aeroseed/urbolienne/2D drawings/DXF/ASD-US000015 - Axe-girouette.DXF

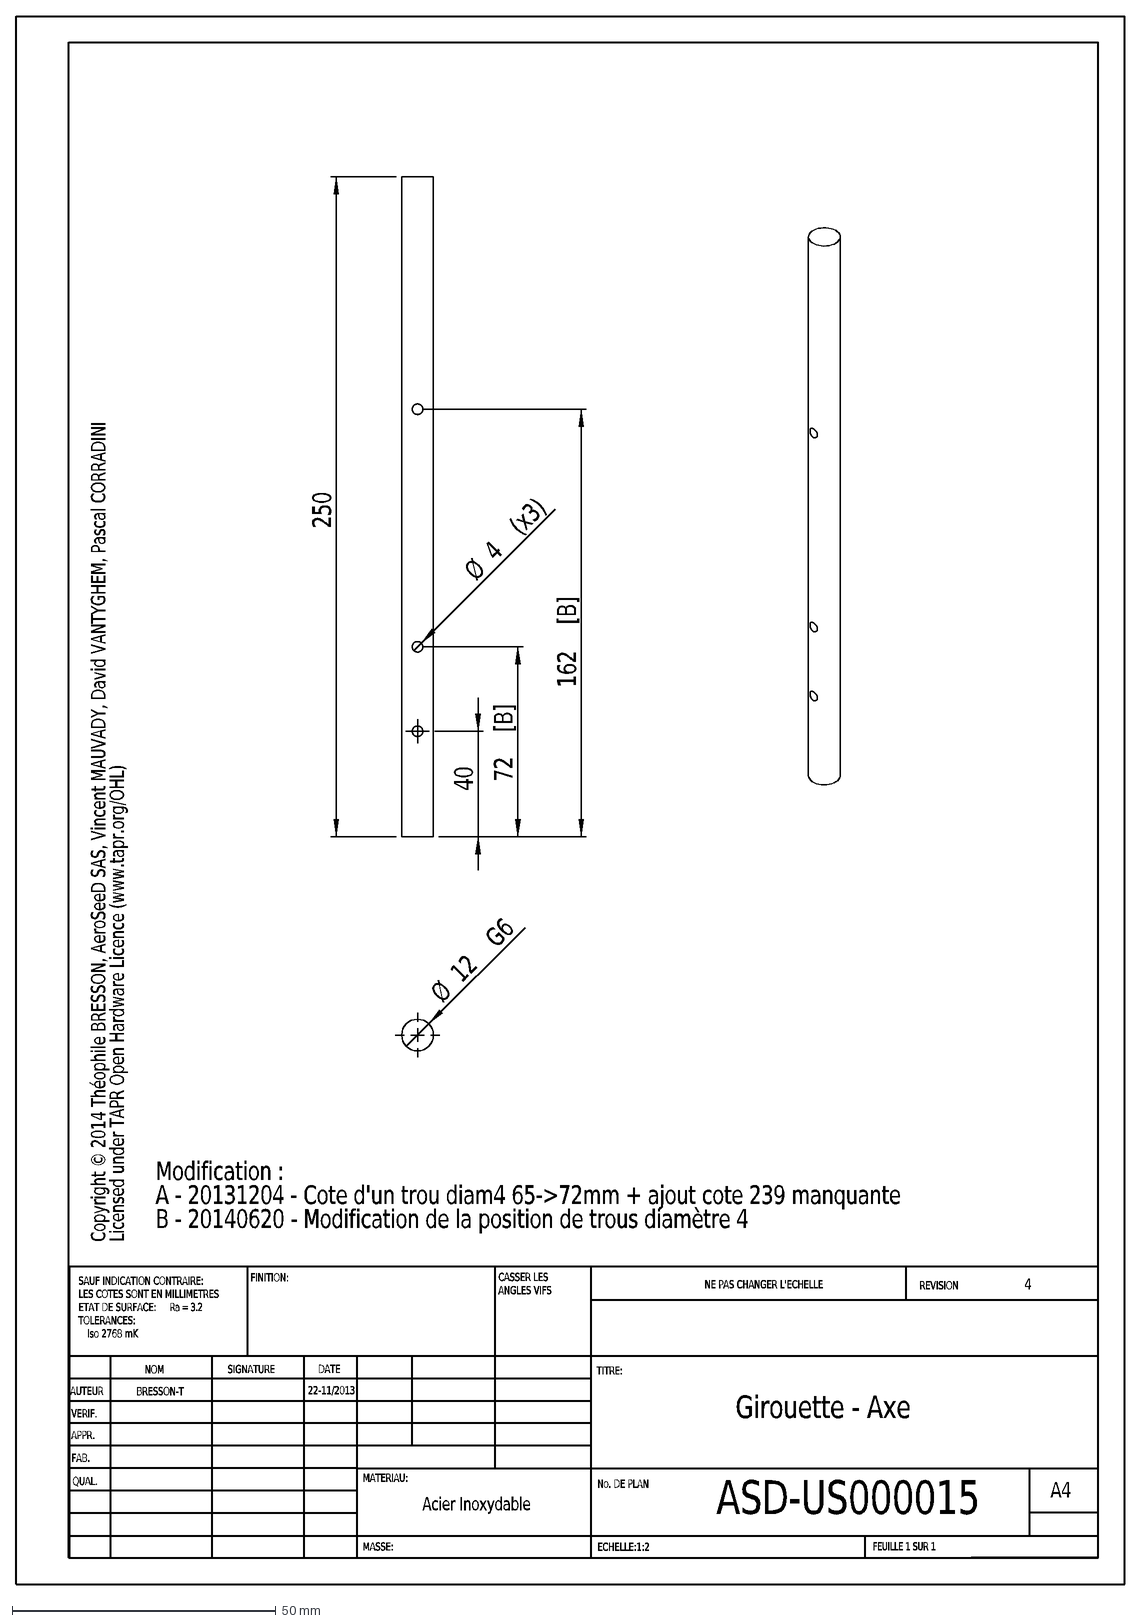
[picture p12: CAD file, 2014-06-24]
2D drawings/DXF/ASD-US000015 - Axe-girouette.DXF
Modification :
A - 20131204 - Cote d'un trou diam4 65->72mm + ajout cote 239 manquante
B - 20140620 - Modification de la position de trous diamètre 4
Copyright © 2014 Théophile BRESSON, AeroSeeD SAS, Vincent MAUVADY, David VANTYGHEM, Pascal CORRADINI
Licensed under TAPR Open Hardware Licence (www.tapr.org/OHL)
4
Girouette - Axe
ASD-US000015
22-11/2013
BRESSON-T
MASSE:
Acier Inoxydable
A4
FEUILLE 1 SUR 1
ECHELLE:1:2
No. DE PLAN
TITRE:
REVISION
NE PAS CHANGER L'ECHELLE
MATERIAU:
DATE
SIGNATURE
NOM
CASSER LES
ANGLES VIFS
FINITION:
QUAL.
FAB.
APPR.
VERIF.
AUTEUR
SAUF INDICATION CONTRAIRE:
LES COTES SONT EN MILLIMETRES
ETAT DE SURFACE:
Ra = 3.2
TOLERANCES:
Iso 2768 mK
40
250
72
[B]
Ø
(x3)
162
12
G6
