aeroseed/urbolienne/2D drawings/PDF/ASD-US000015 - Axe-girouette.PDF

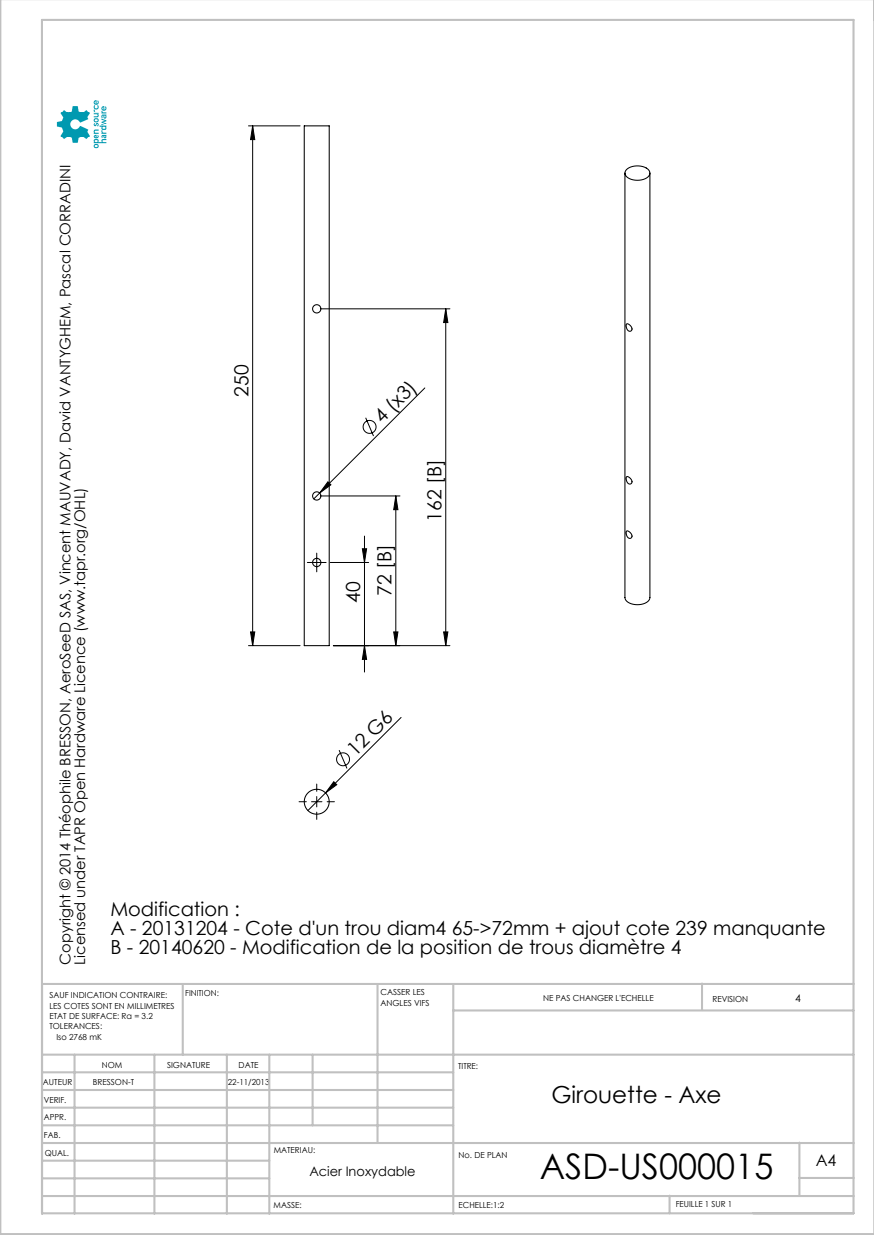
[picture p19: page 1]
ECHELLE:1:2; FEUILLE 1 SUR 1; NE PAS CHANGER L'ECHELLE; REVISION; CASSER LES ANGLES VIFS

Copyright © 2014 Théophile BRESSON, AeroSeeD SAS, Vincent MAUVADY, David VANTYGHEM, Pascal CORRADINI

Licensed under TAPR Open Hardware Licence (www.tapr.org/OHL)

Modification :
A - 20131204 - Cote d'un trou diam4 65->72mm + ajout cote 239 manquante
B - 20140620 - Modification de la position de trous diamètre 4

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

NOM | SIGNATURE | DATE | | | | TITRE: Girouette - Axe
QUAL. | | | | MATERIAU: Acier Inoxydable | ASD-US000015 No. DE PLAN | A4

AUTEUR | BRESSON-T | | 22-11/2013
VERIF.
APPR.
FAB.
