aeroseed/urbolienne/2D drawings/PDF/ASD-US000028 - Alternateur-rotor-CORADINI.PDF

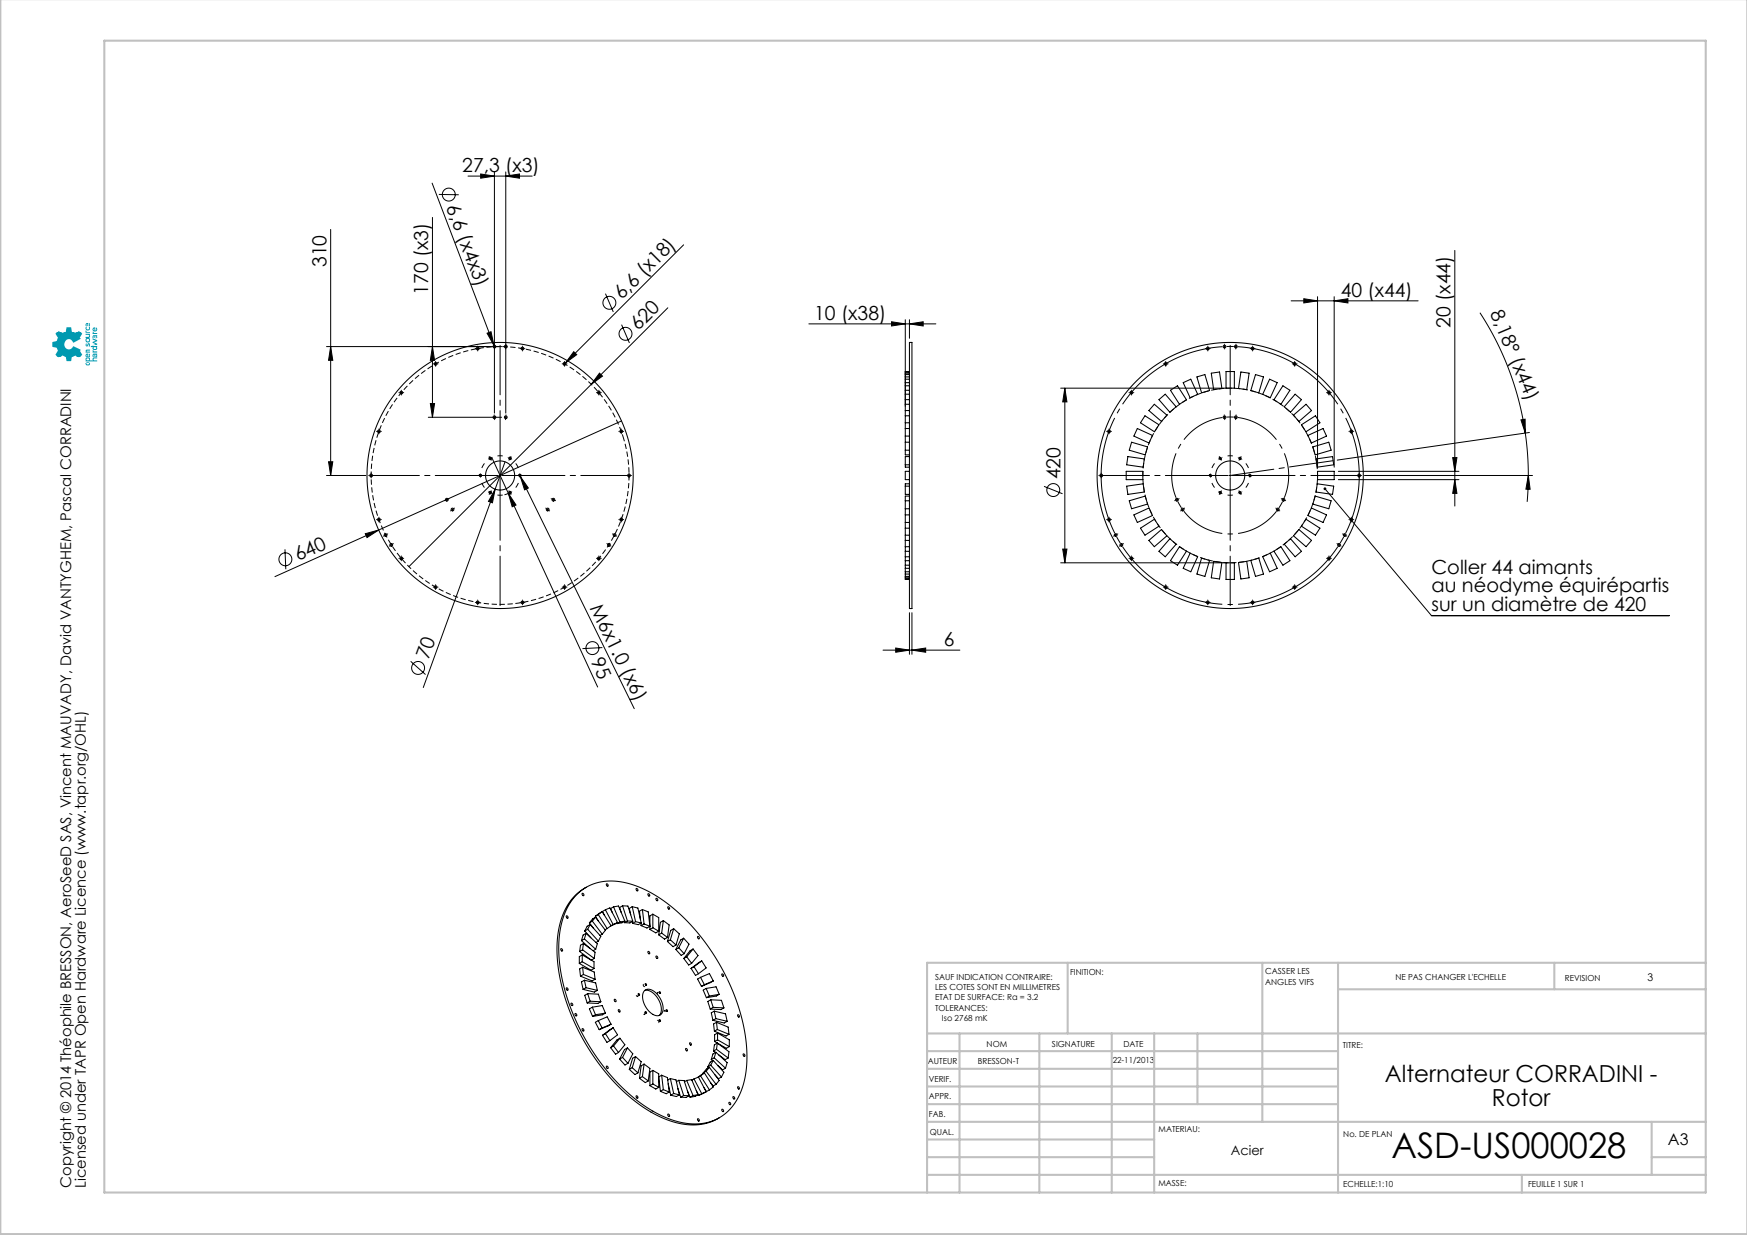
[picture p20: page 1]
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

Copyright © 2014 Théophile BRESSON, AeroSeeD SAS, Vincent MAUVADY, David VANTYGHEM, Pascal CORRADINI

Coller 44 aimants
au néodyme équirépartis
sur un diamètre de 420

Licensed under TAPR Open Hardware Licence (www.tapr.org/OHL)

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

NOM | SIGNATURE | DATE | | | | TITRE: Alternateur CORRADINI -Rotor
QUAL. | | | | MATERIAU: Acier | ASD-US000028 No. DE PLAN | A3

AUTEUR | BRESSON-T | | 22-11/2013
VERIF.
APPR.
FAB.
