aeroseed/urbolienne/2D drawings/PDF/ASD-US000031 - Arbre-transmission-pale.PDF

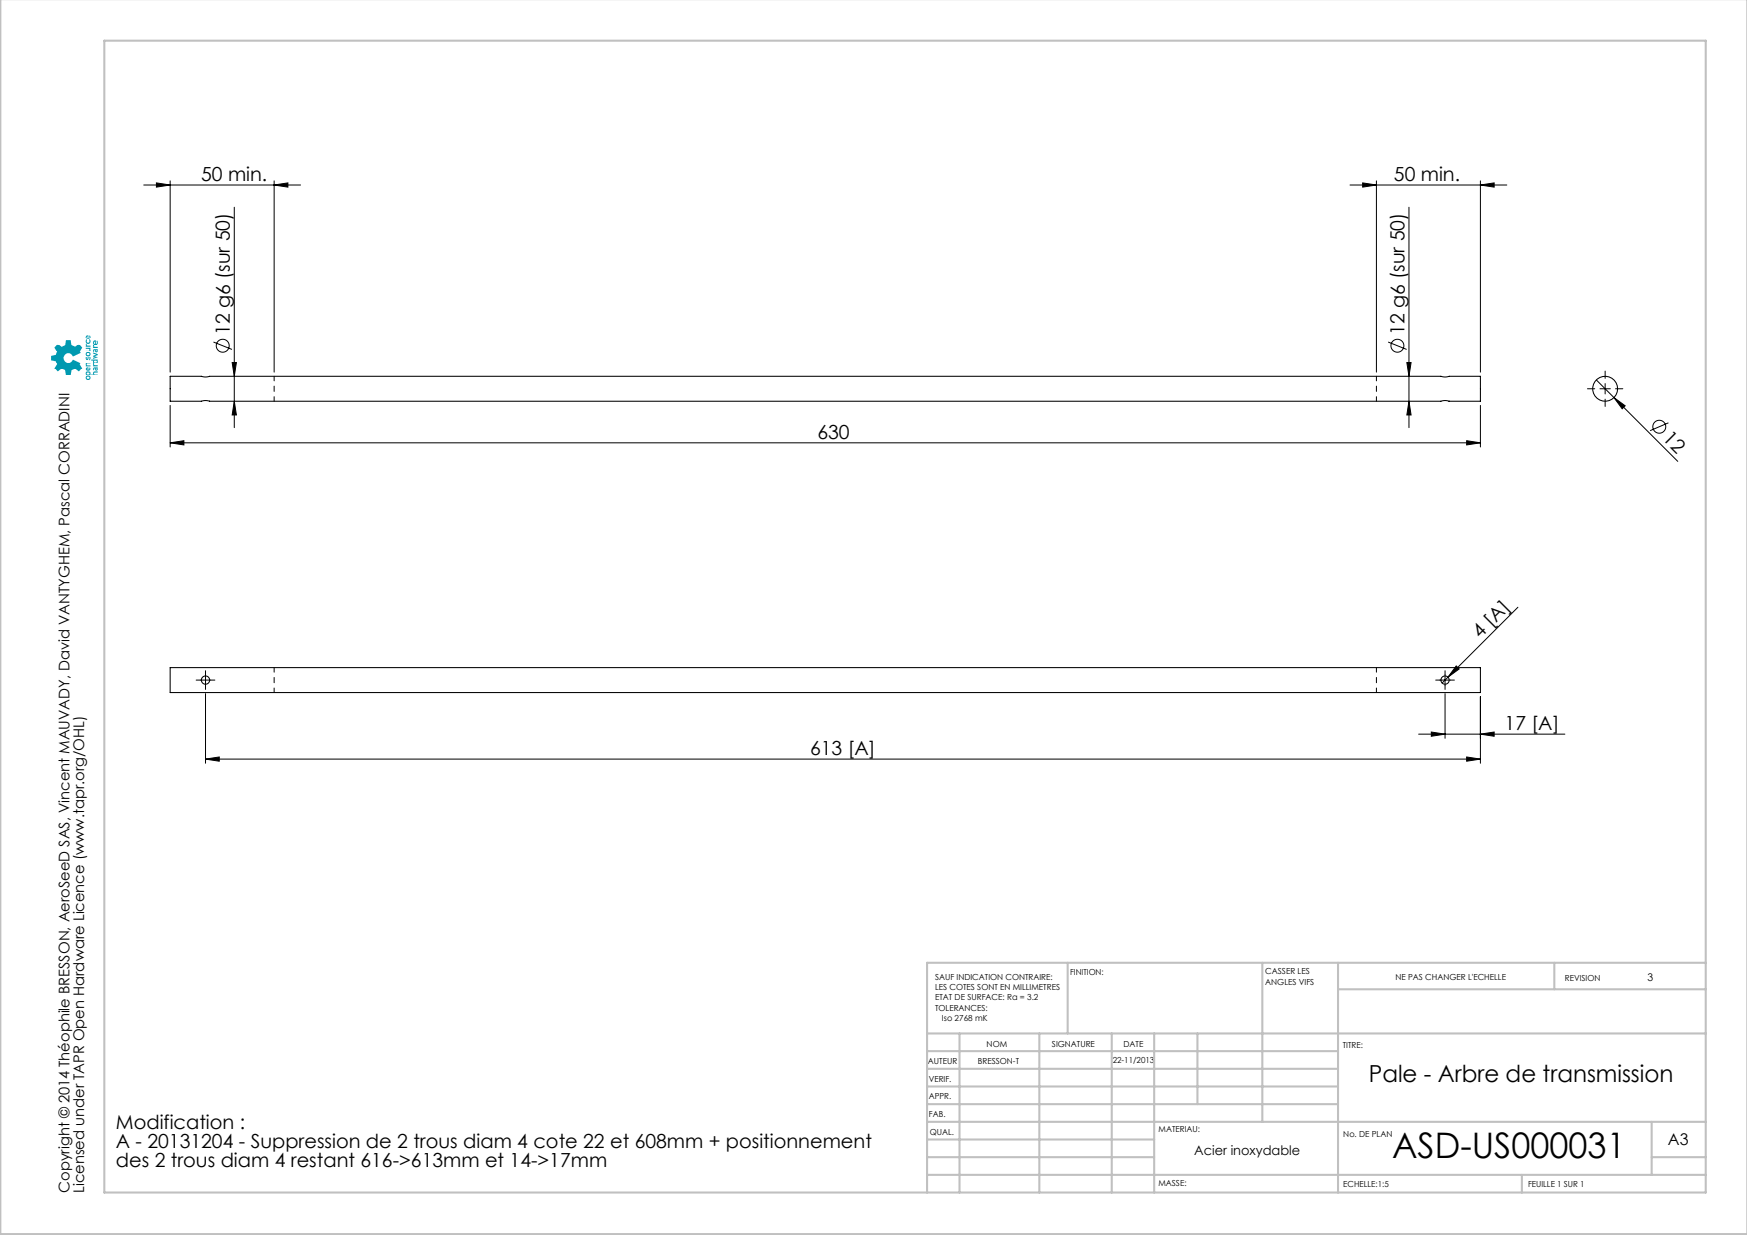
[picture p21: page 1]
12 g6 (sur 50); 50 min.; ECHELLE:1:5; FEUILLE 1 SUR 1; NE PAS CHANGER L'ECHELLE; REVISION; CASSER LES ANGLES VIFS

Copyright © 2014 Théophile BRESSON, AeroSeeD SAS, Vincent MAUVADY, David VANTYGHEM, Pascal CORRADINI

Licensed under TAPR Open Hardware Licence (www.tapr.org/OHL)

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

NOM | SIGNATURE | DATE | | | | TITRE: Pale - Arbre de transmission
QUAL. | | | | MATERIAU: Acier inoxydable | ASD-US000031 No. DE PLAN | A3

AUTEUR | BRESSON-T | | 22-11/2013
VERIF.
APPR.
FAB.

Modification :
A - 20131204 - Suppression de 2 trous diam 4 cote 22 et 608mm + positionnement
des 2 trous diam 4 restant 616->613mm et 14->17mm
