aeroseed/urbolienne/2D drawings/PDF/ASD-US000036 - Plateau-Axe-fixe.PDF

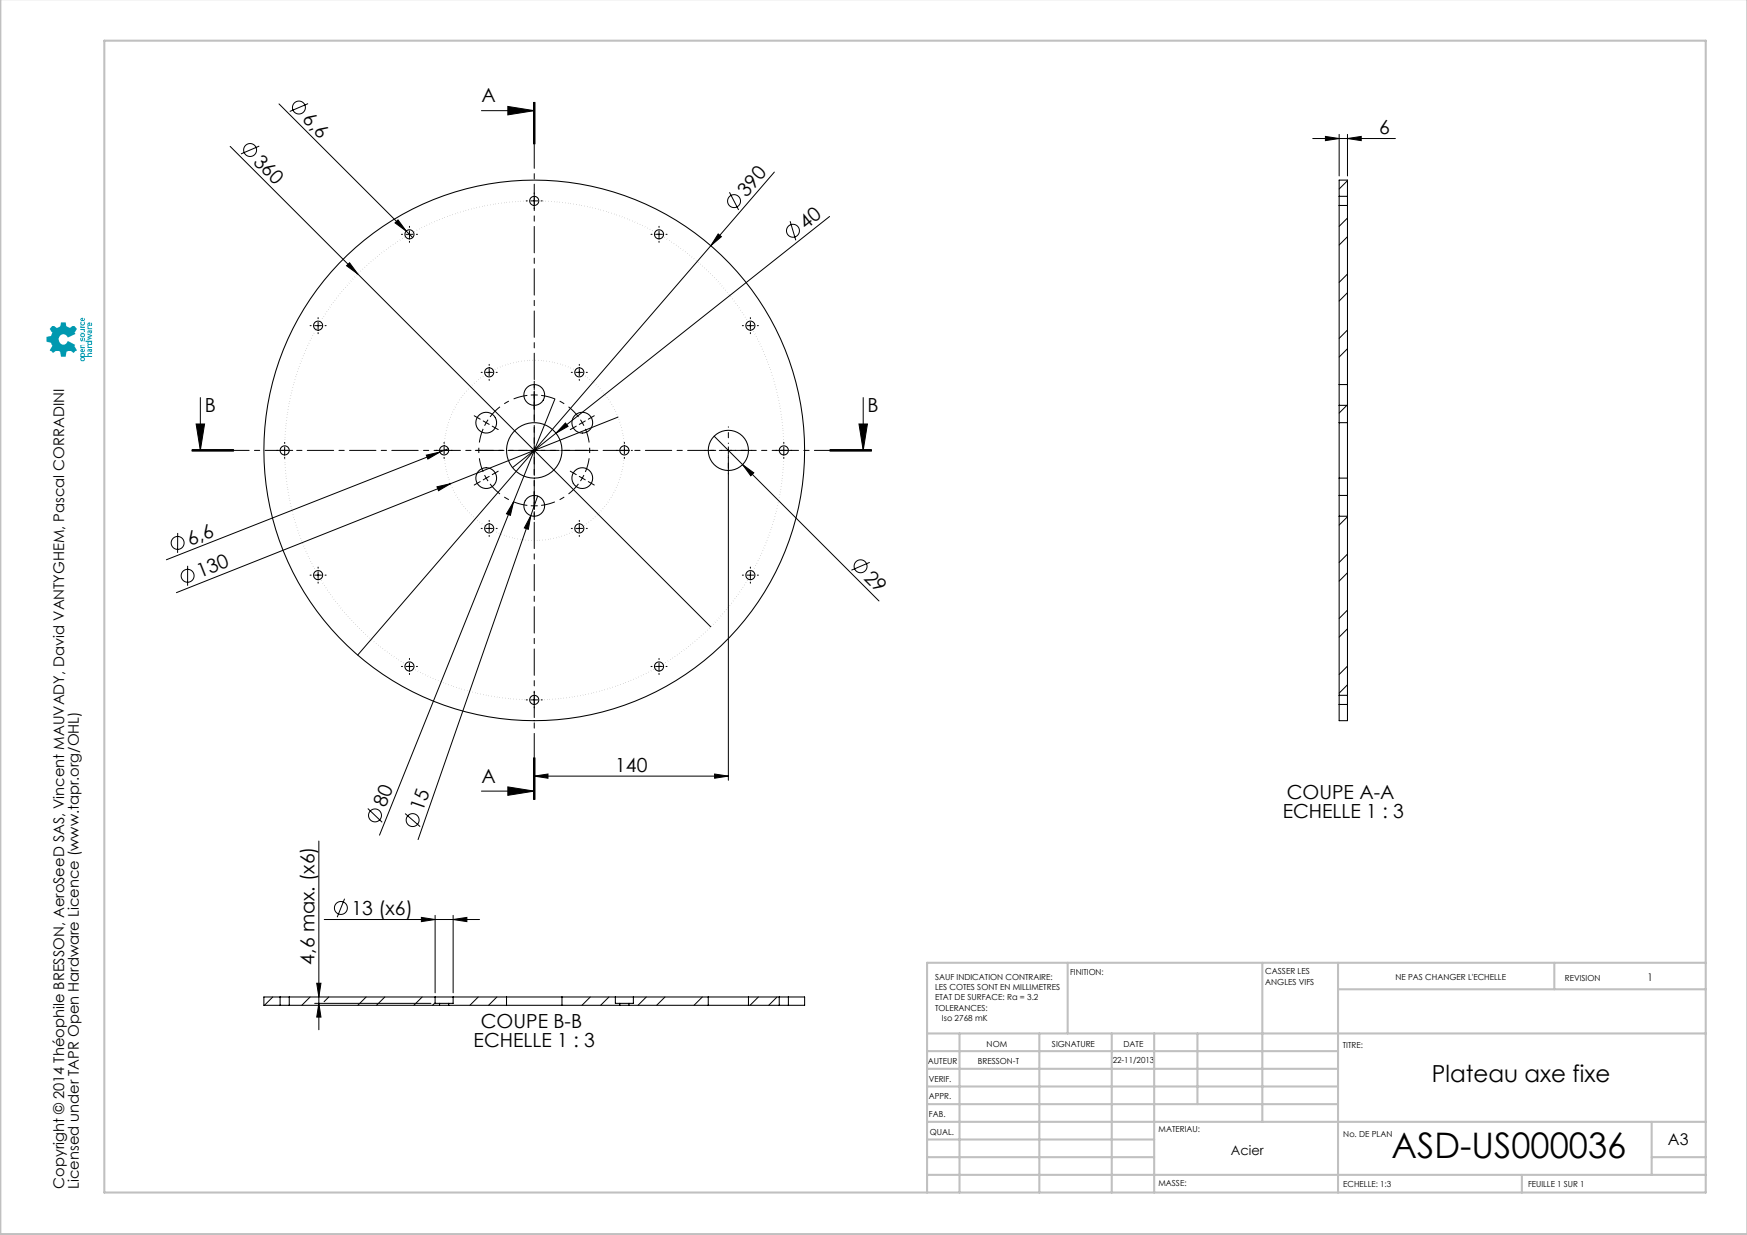
[picture p22: page 1]
COUPE A-A ECHELLE 1 : 3; 4,6 max. (x6); COUPE B-B ECHELLE 1 : 3; ECHELLE: 1:3; FEUILLE 1 SUR 1; NE PAS CHANGER L'ECHELLE; REVISION; CASSER LES ANGLES VIFS

Copyright © 2014 Théophile BRESSON, AeroSeeD SAS, Vincent MAUVADY, David VANTYGHEM, Pascal CORRADINI

Licensed under TAPR Open Hardware Licence (www.tapr.org/OHL)

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

NOM | SIGNATURE | DATE | | | | TITRE: Plateau axe fixe
QUAL. | | | | MATERIAU: Acier | ASD-US000036 No. DE PLAN | A3

AUTEUR | BRESSON-T | | 22-11/2013
VERIF.
APPR.
FAB.
