aeroseed/urbolienne/2D drawings/PDF/ASD-US000037 - Axe-Pale.PDF

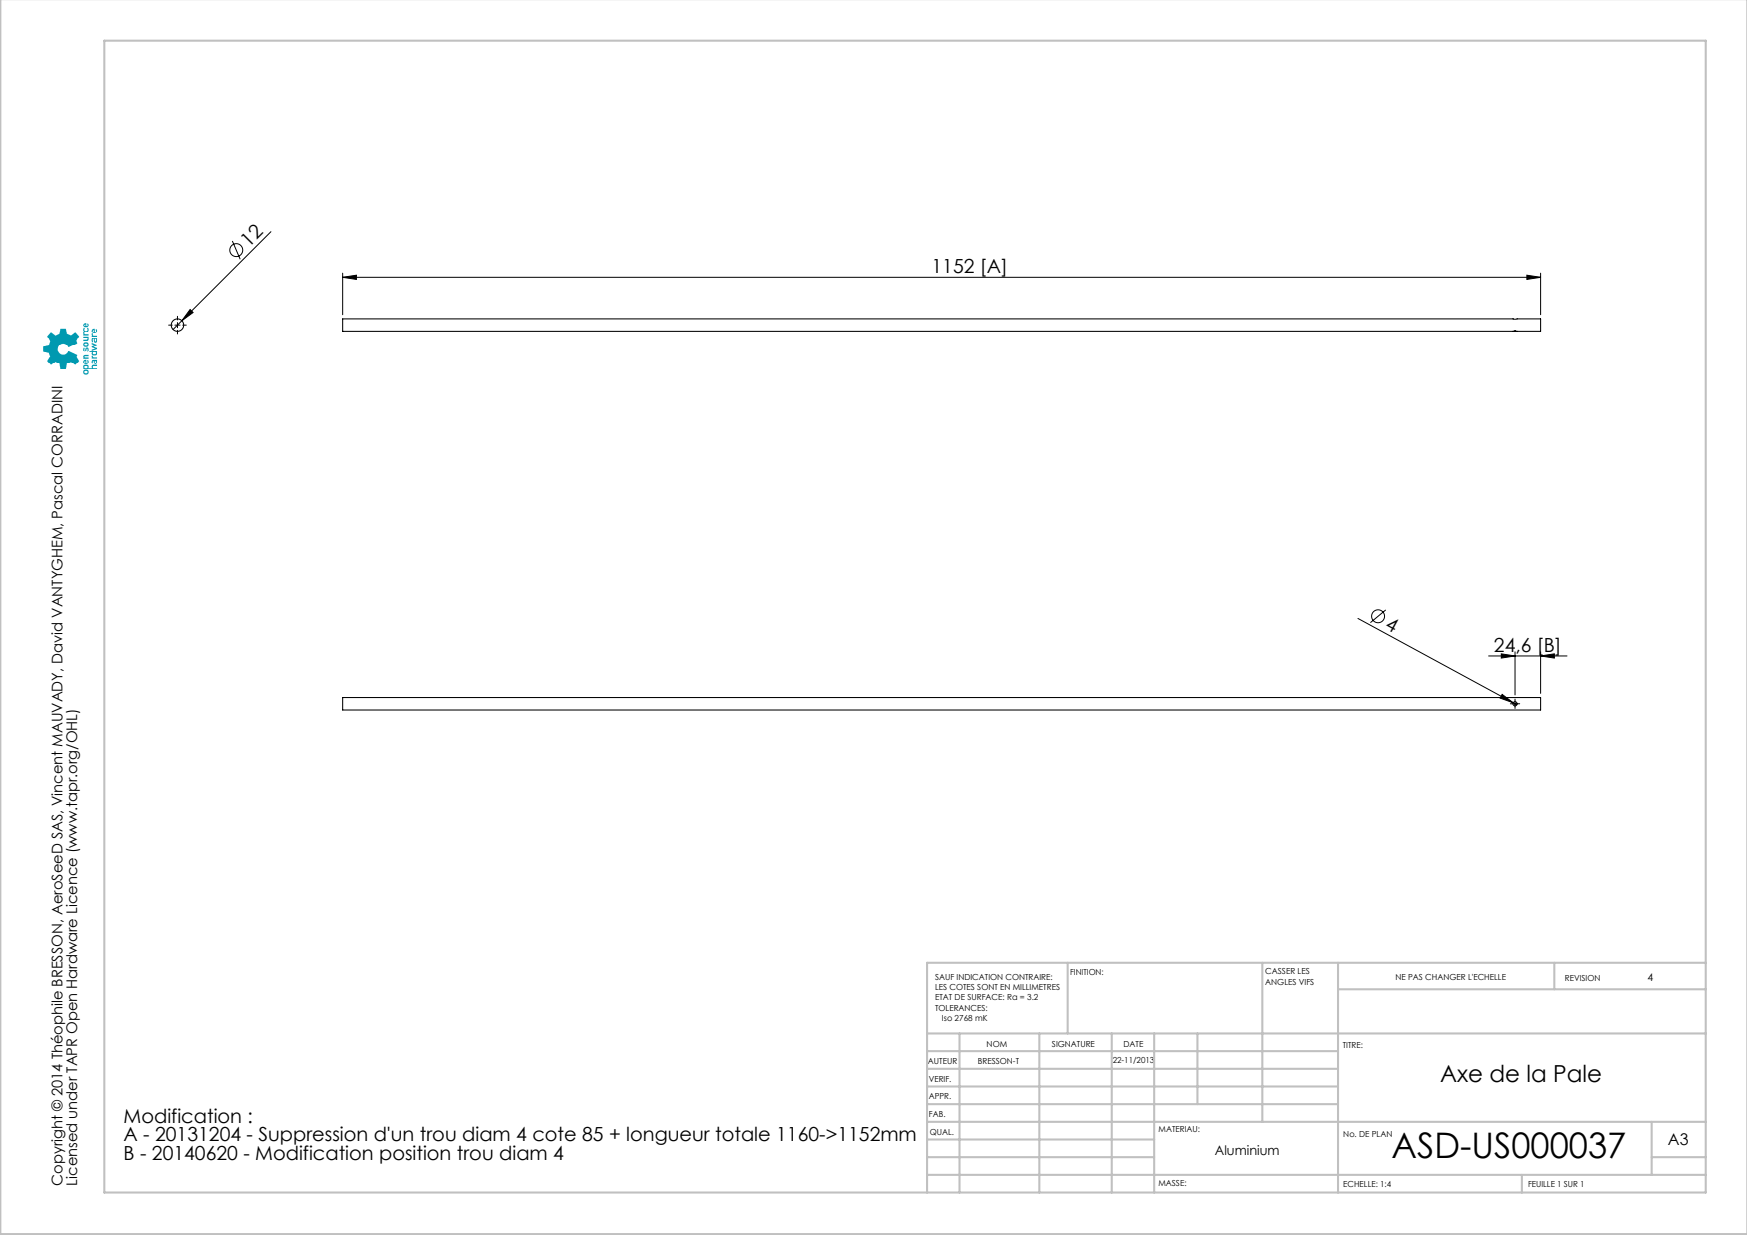
[picture p23: page 1]
ECHELLE: 1:4; FEUILLE 1 SUR 1; NE PAS CHANGER L'ECHELLE; REVISION; CASSER LES ANGLES VIFS

Copyright © 2014 Théophile BRESSON, AeroSeeD SAS, Vincent MAUVADY, David VANTYGHEM, Pascal CORRADINI

Licensed under TAPR Open Hardware Licence (www.tapr.org/OHL)

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

NOM | SIGNATURE | DATE | | | | TITRE: Axe de la Pale
QUAL. | | | | MATERIAU: Aluminium | ASD-US000037 No. DE PLAN | A3

AUTEUR | BRESSON-T | | 22-11/2013
VERIF.
APPR.
FAB.

Modification :
A - 20131204 - Suppression d'un trou diam 4 cote 85 + longueur totale 1160->1152mm
B - 20140620 - Modification position trou diam 4
