aeroseed/urbolienne/2D drawings/PDF/ASD-US000014 - Girouette.PDF

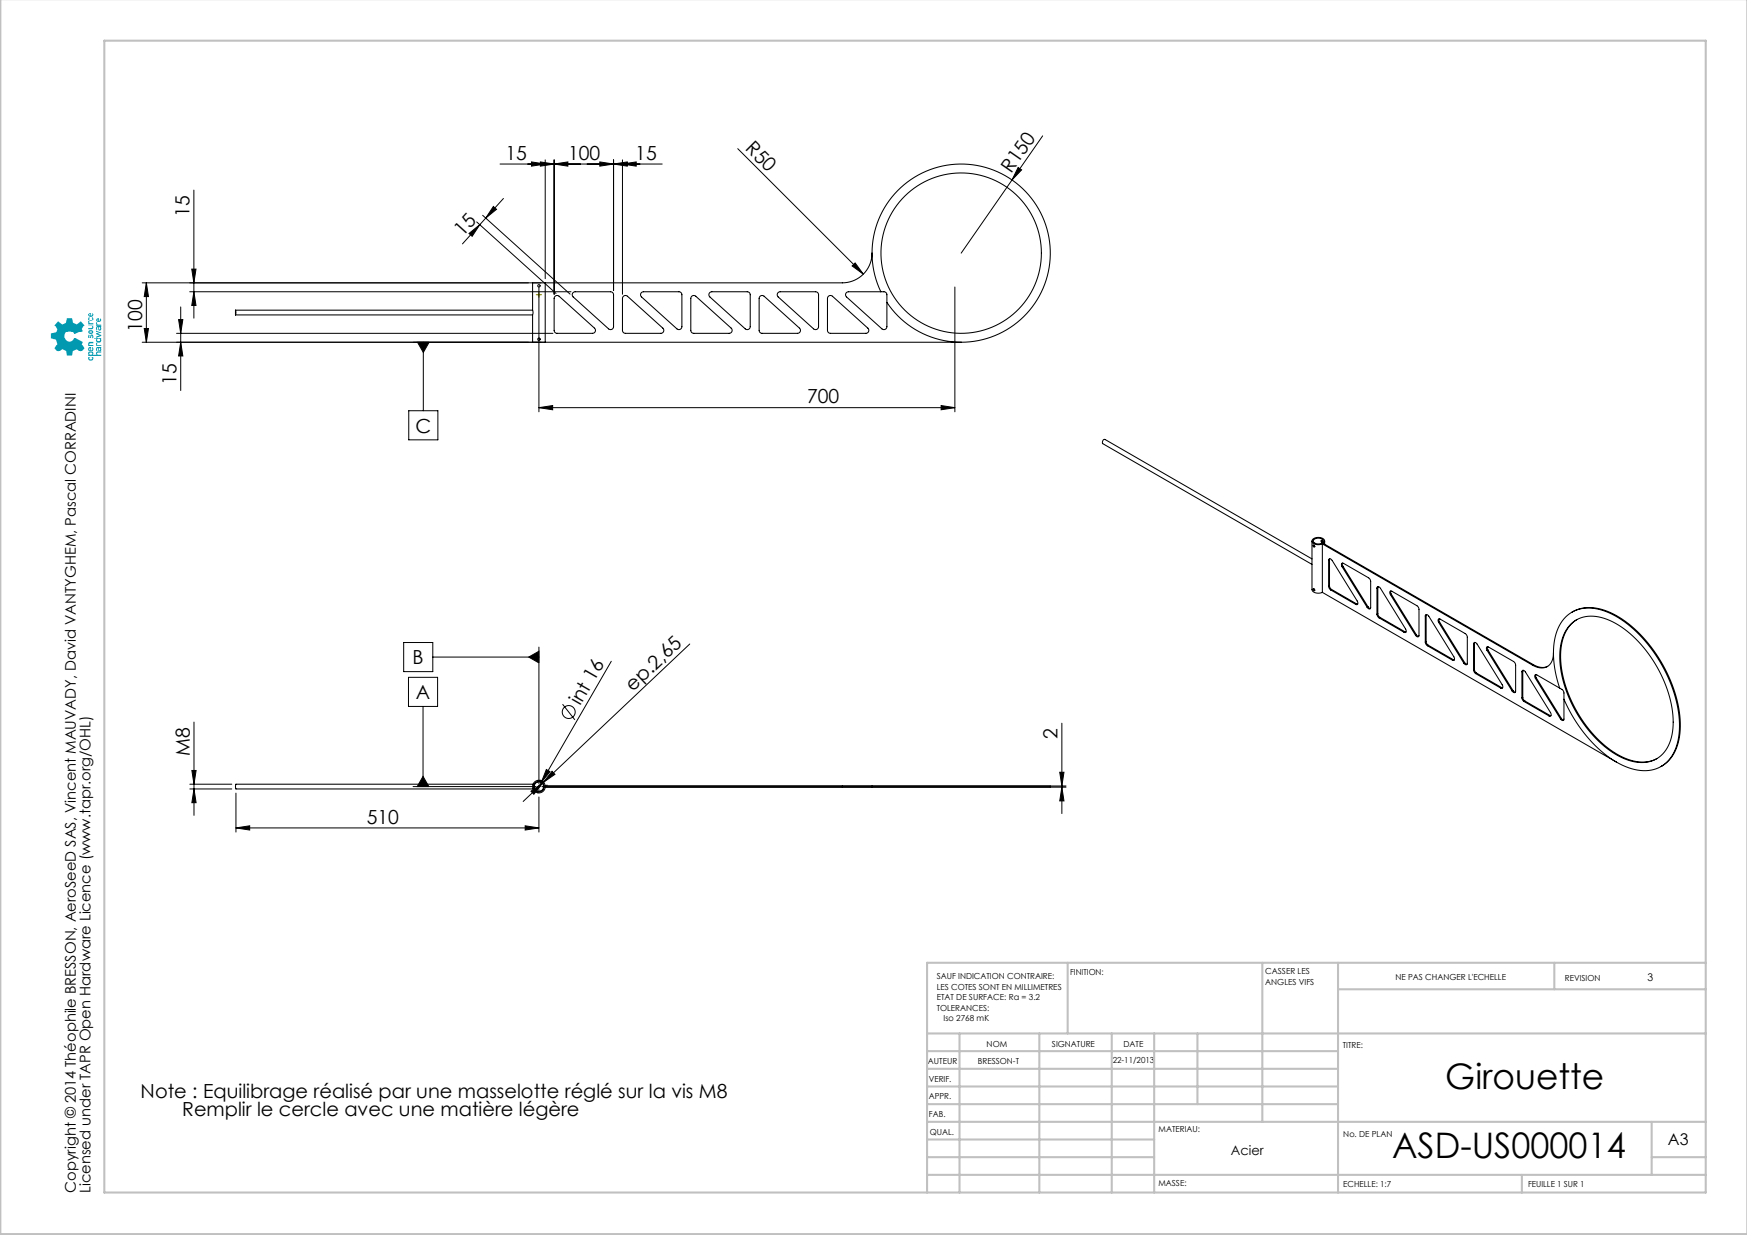
[picture p26: page 1]
int 16; ECHELLE: 1:7; FEUILLE 1 SUR 1; NE PAS CHANGER L'ECHELLE; REVISION; CASSER LES ANGLES VIFS

Copyright © 2014 Théophile BRESSON, AeroSeeD SAS, Vincent MAUVADY, David VANTYGHEM, Pascal CORRADINI

Licensed under TAPR Open Hardware Licence (www.tapr.org/OHL)

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

NOM | SIGNATURE | DATE | | | | TITRE: Girouette
QUAL. | | | | MATERIAU: Acier | ASD-US000014 No. DE PLAN | A3

AUTEUR | BRESSON-T | | 22-11/2013
VERIF.
APPR.
FAB.

Note : Equilibrage réalisé par une masselotte réglé sur la vis M8 Remplir le cercle avec une matière légère
