aeroseed/urbolienne/2D drawings/PDF/ASD-US000027 - Bobinage generatrice.PDF

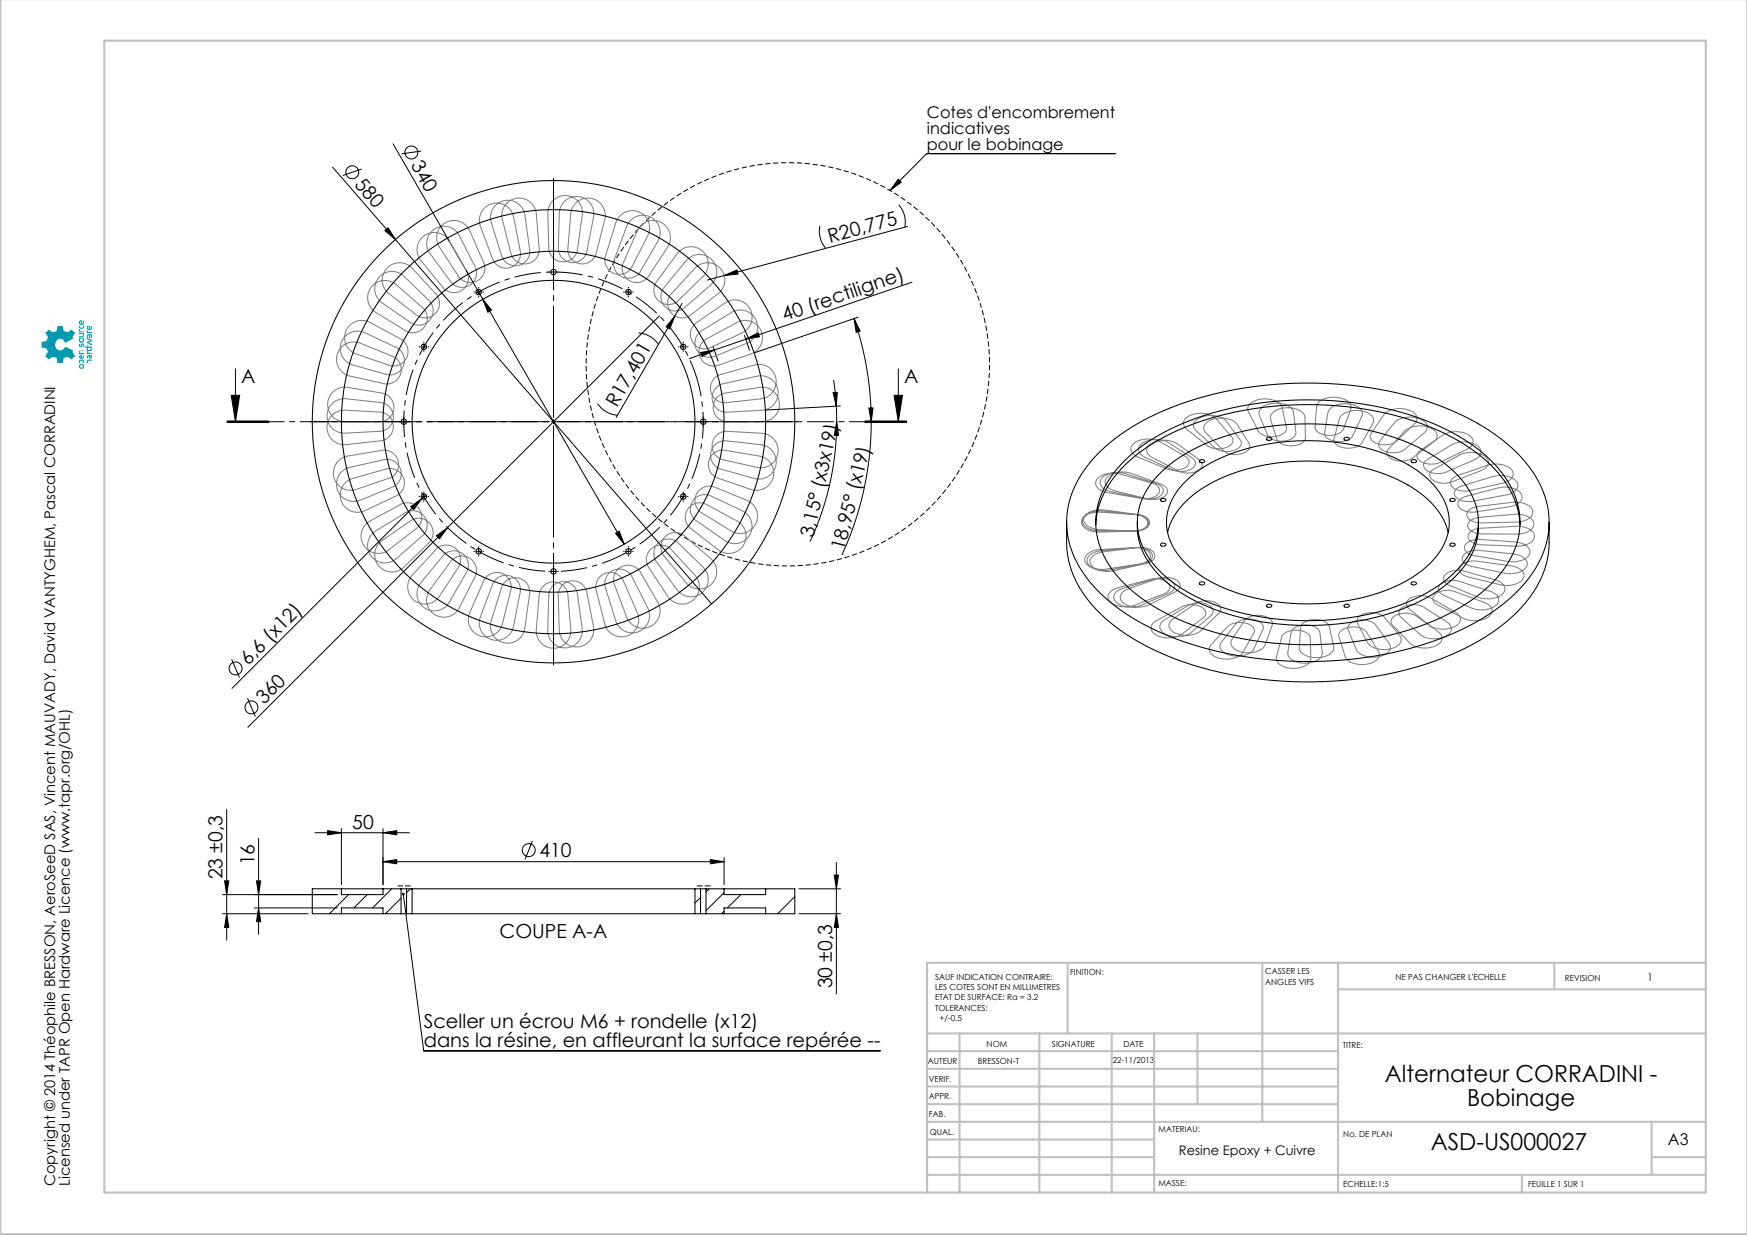
[picture p27: page 1]
40 (rectiligne); COUPE A-A; ECHELLE:1:5; FEUILLE 1 SUR 1; NE PAS CHANGER L'ECHELLE; REVISION; CASSER LES ANGLES VIFS

Cotes d'encombrement
indicatives
pour le bobinage

Copyright © 2014 Théophile BRESSON, AeroSeeD SAS, Vincent MAUVADY, David VANTYGHEM, Pascal CORRADINI

Licensed under TAPR Open Hardware Licence (www.tapr.org/OHL)

SAUF INDICATION CONTRAIRE:
LES COTES SONT EN MILLIMETRES
ETAT DE SURFACE: Ra = 3.2
TOLERANCES:

Sceller un écrou M6 + rondelle (x12)
dans la résine, en affleurant la surface repérée --

NOM | SIGNATURE | DATE | | | | TITRE: Alternateur CORRADINI -Bobinage

AUTEUR | BRESSON-T | | 22-11/2013
VERIF.
APPR.
FAB.
QUAL. | | | | MATERIAU: Resine Epoxy + Cuivre | No. DE PLAN ASD-US000027 | A3
